CedarGroveStudios/PCB_PCM510xA_I2S_DAC/media/Screenshot 2023-10-17 at 11.07.14 PM.png

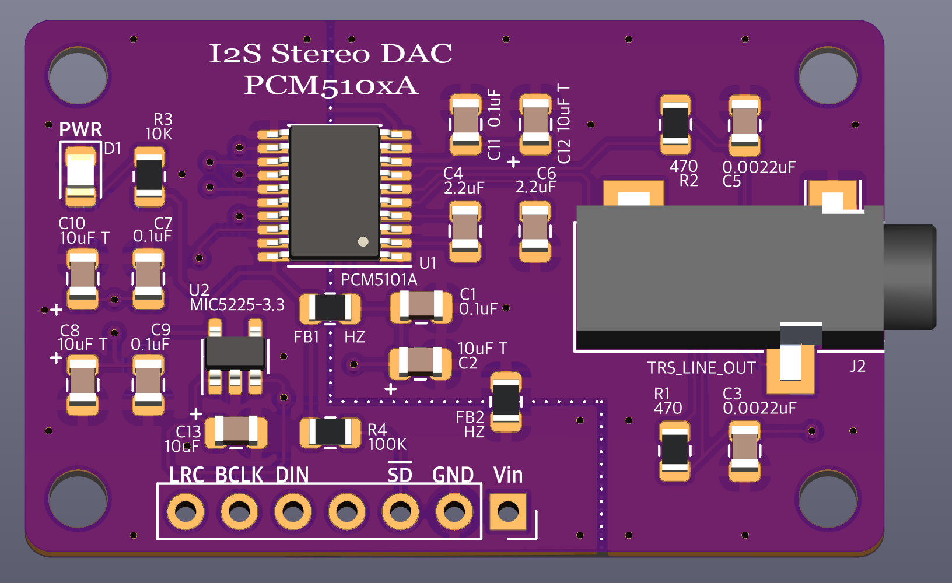
media/Screenshot 2023-10-17 at 11.07.14 PM.png
